yo5ptd/xt-cf-pico/KiCad/xt-cf back.png

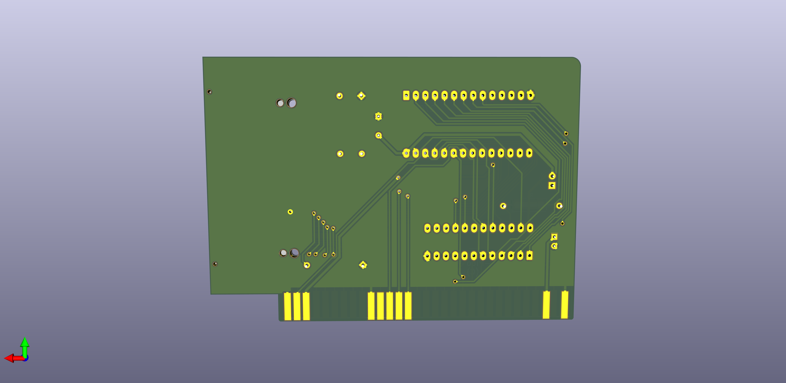
KiCad/xt-cf back.png
