yo5ptd/xt-cf-pico/KiCad/xt-cf front.png

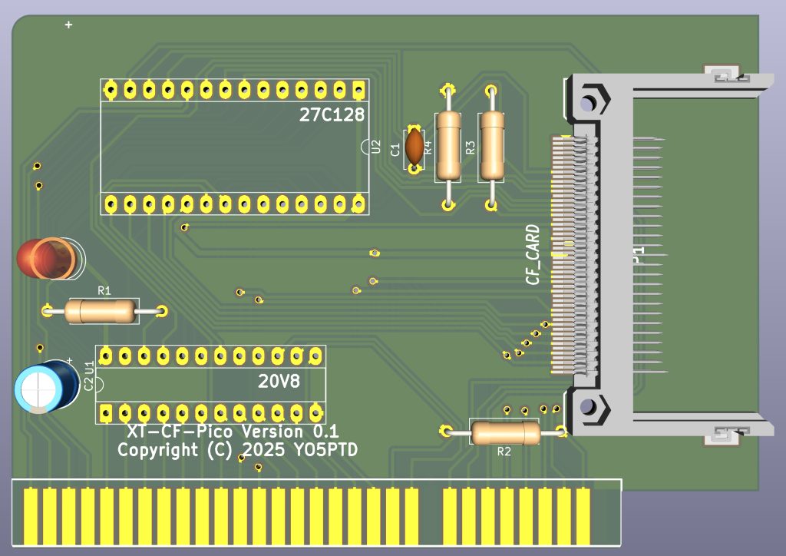
KiCad/xt-cf front.png
